nat-tsang/mte380/PlatformIO_codebase/include/PIDController.h

#pragma once
#include <Arduino.h>

class PIDController {
private:
    float Kp, Ki, Kd;
    float integral;
    double previousError;
    unsigned long lastTime;

public:
    PIDController(float p, float i, float d);
    double compute(float error);
    void reset();  // clear integral/prev error
    void setGains(float p, float i, float d);  // update PID gains dynamically
};
